OsamaAlsahli/data-glove/images/gantt_chart.png

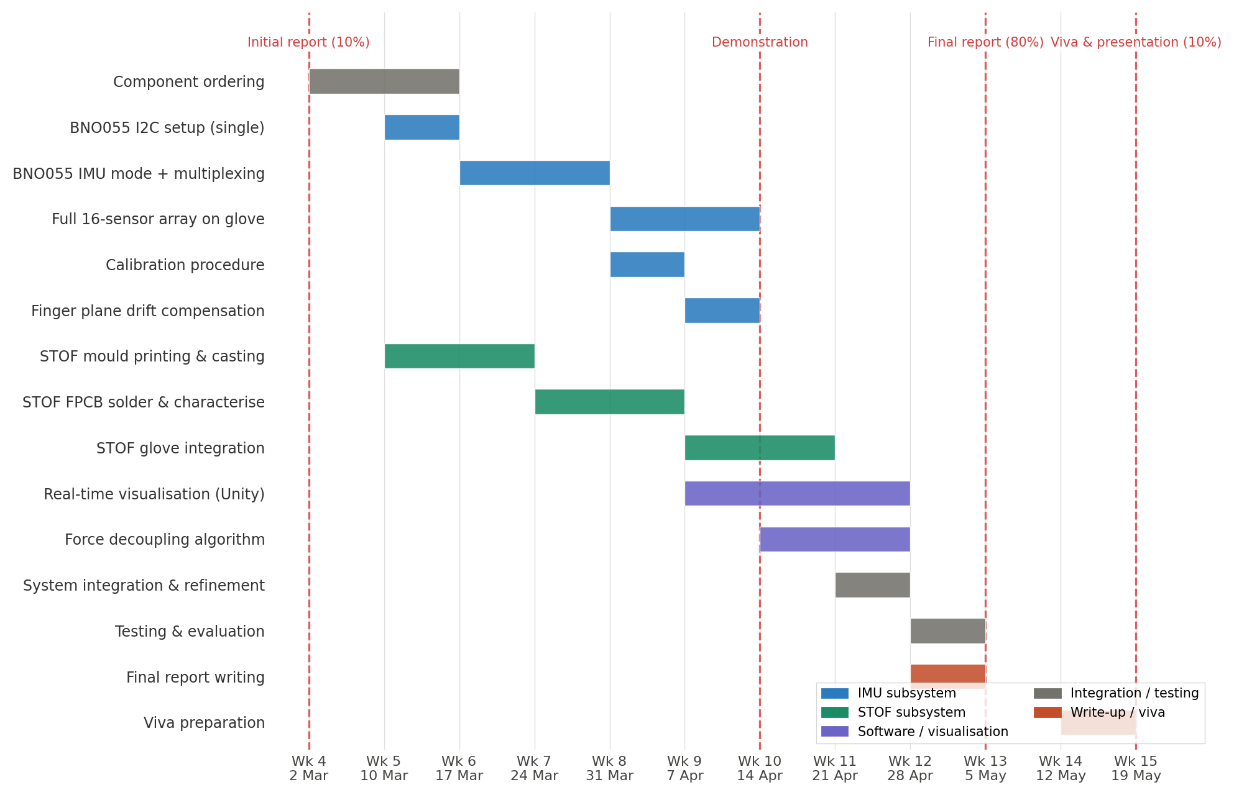
images/gantt_chart.png
