OsamaAlsahli/data-glove/images/PXL_20260508_102140044.jpg

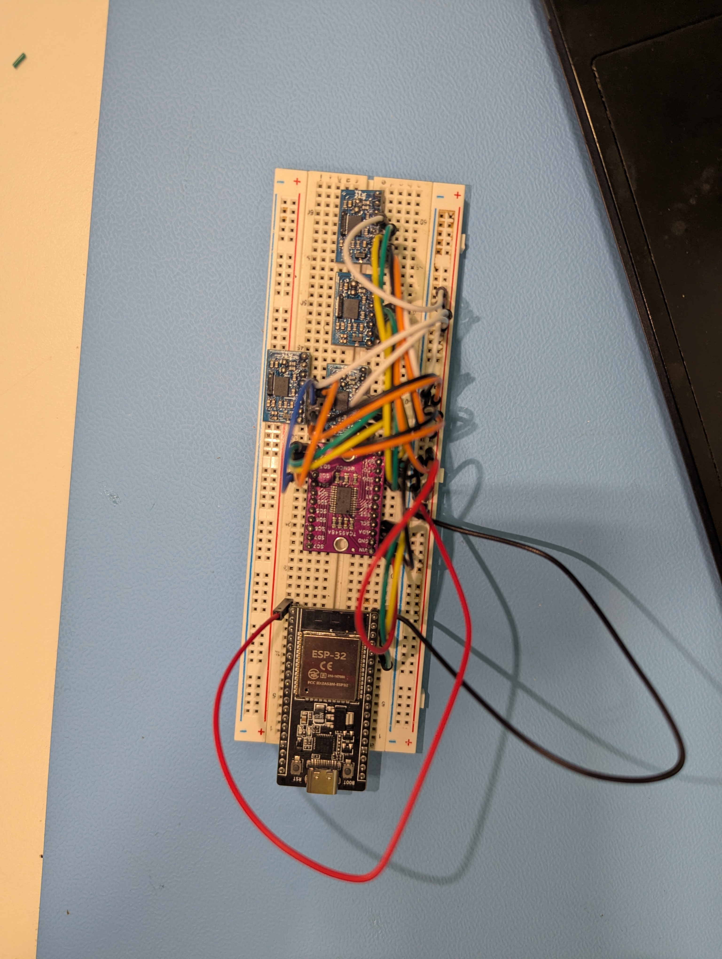
images/PXL_20260508_102140044.jpg
