OsamaAlsahli/data-glove/images/PXL_20260508_141840744.jpg

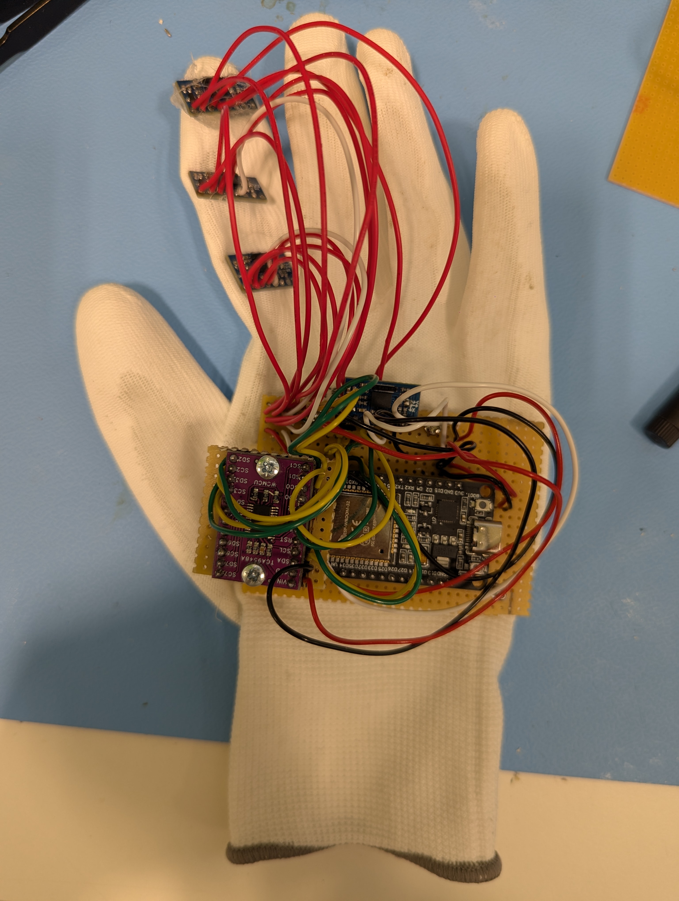
images/PXL_20260508_141840744.jpg
