OsamaAlsahli/data-glove/images/PXL_20260508_141846778.jpg

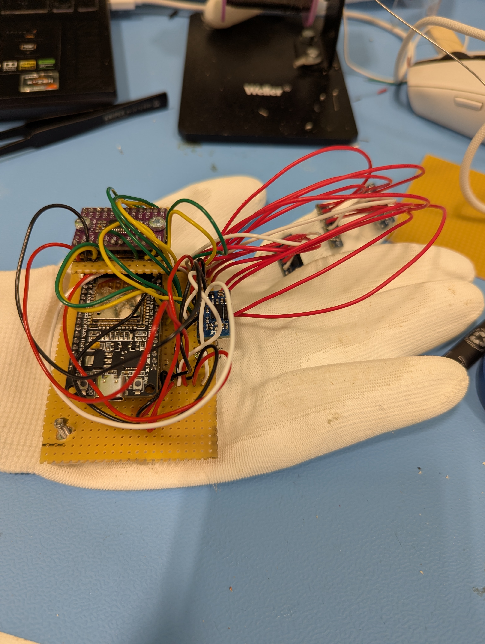
images/PXL_20260508_141846778.jpg
