OsamaAlsahli/data-glove/images/PXL_20260508_141911992.jpg

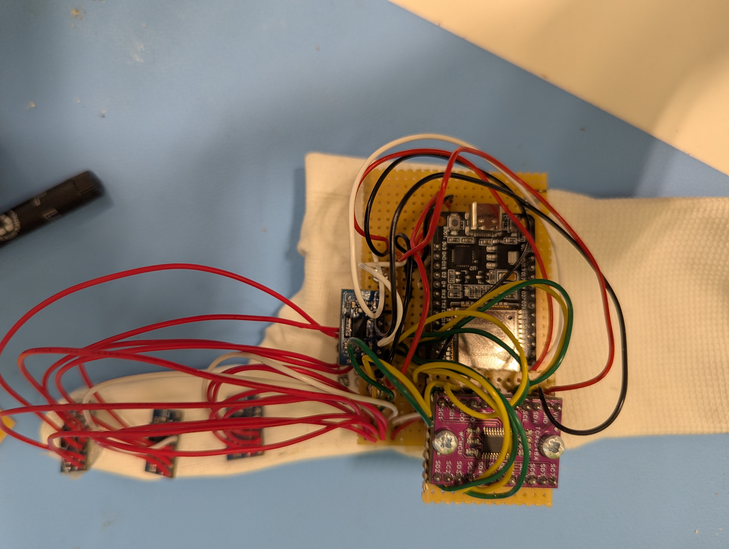
images/PXL_20260508_141911992.jpg
