OsamaAlsahli/data-glove/images/PXL_20260508_141916743.jpg

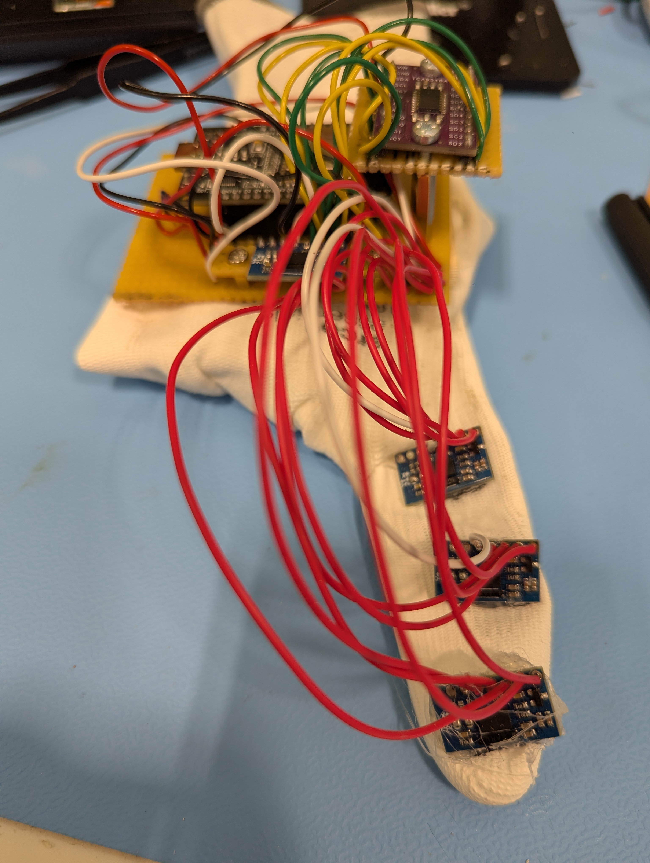
images/PXL_20260508_141916743.jpg
