OsamaAlsahli/data-glove/images/PXL_20260508_141919534.jpg

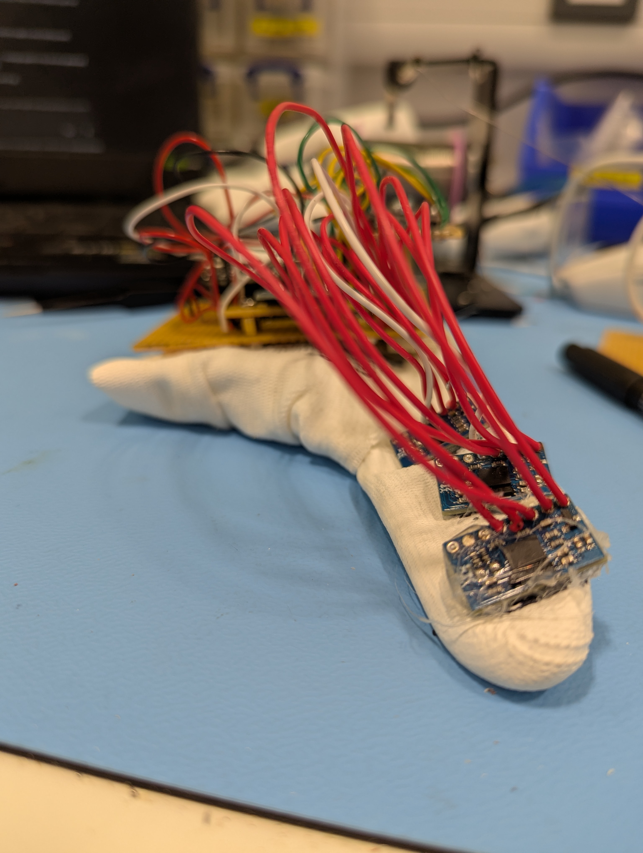
images/PXL_20260508_141919534.jpg
