OsamaAlsahli/data-glove/images/PXL_20260508_141922260.jpg

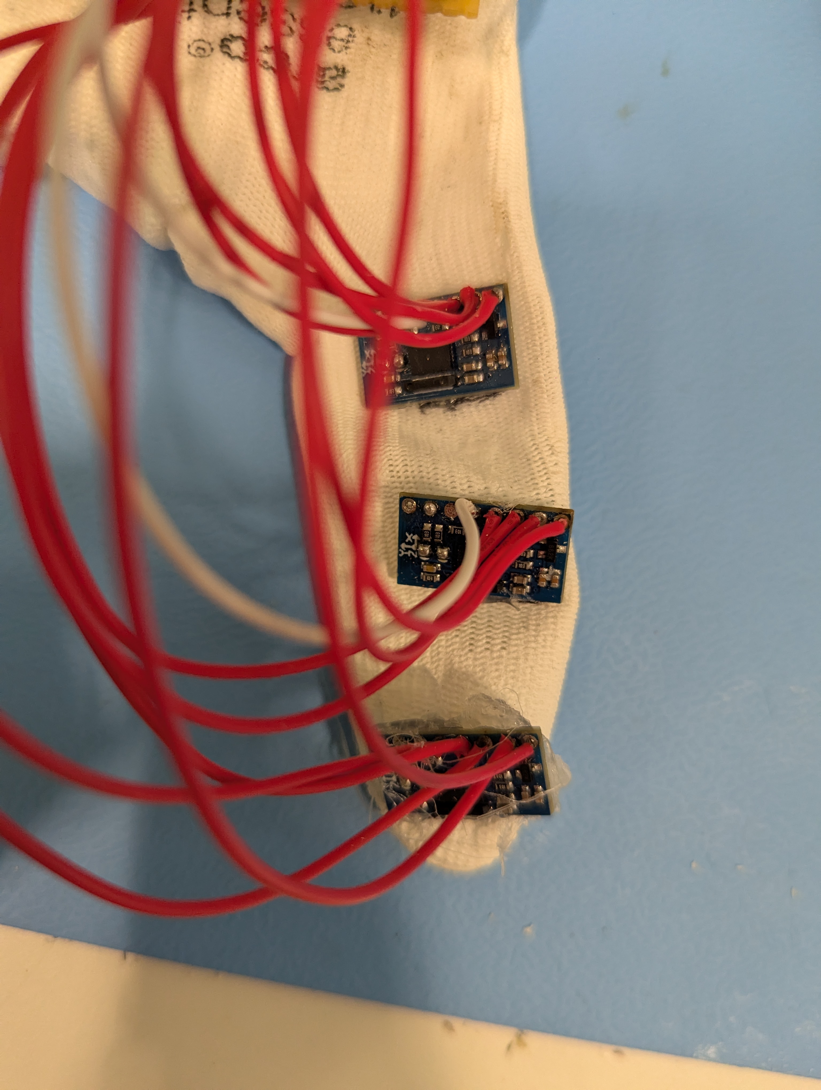
images/PXL_20260508_141922260.jpg
