OsamaAlsahli/data-glove/images/PXL_20260508_142635021.jpg

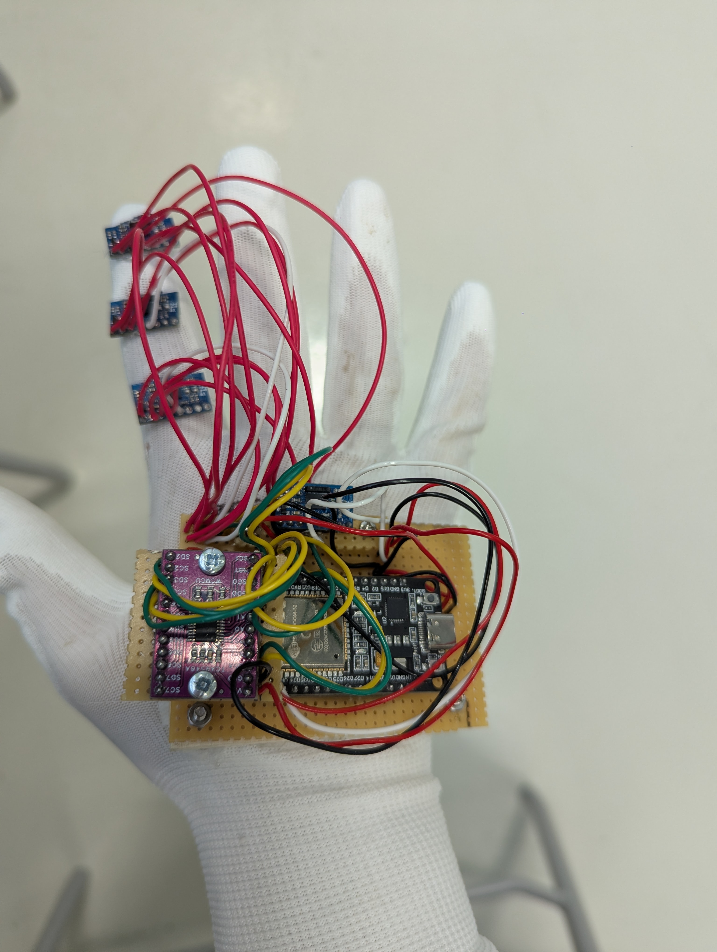
images/PXL_20260508_142635021.jpg
