OsamaAlsahli/data-glove/images/PXL_20260508_142637058.jpg

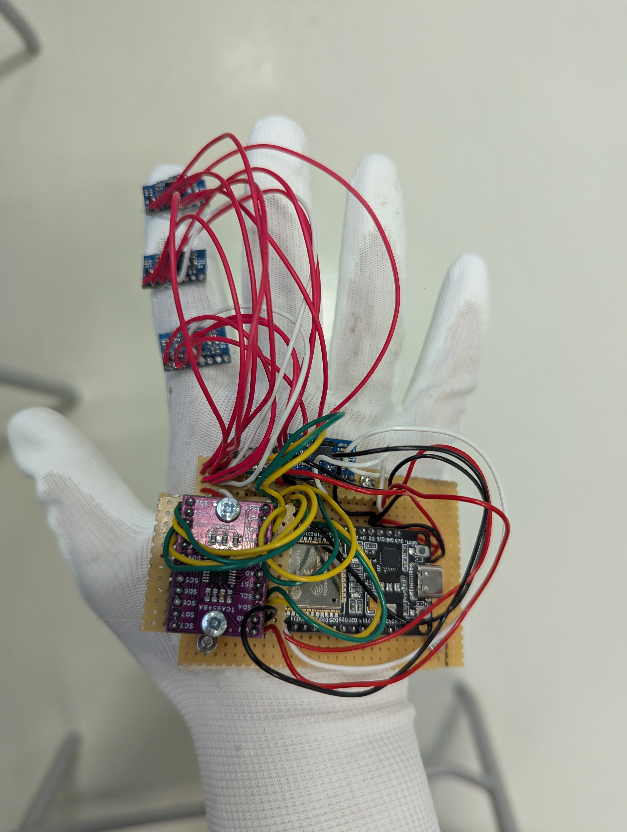
images/PXL_20260508_142637058.jpg
