OsamaAlsahli/data-glove/images/PXL_20260508_142641269.jpg

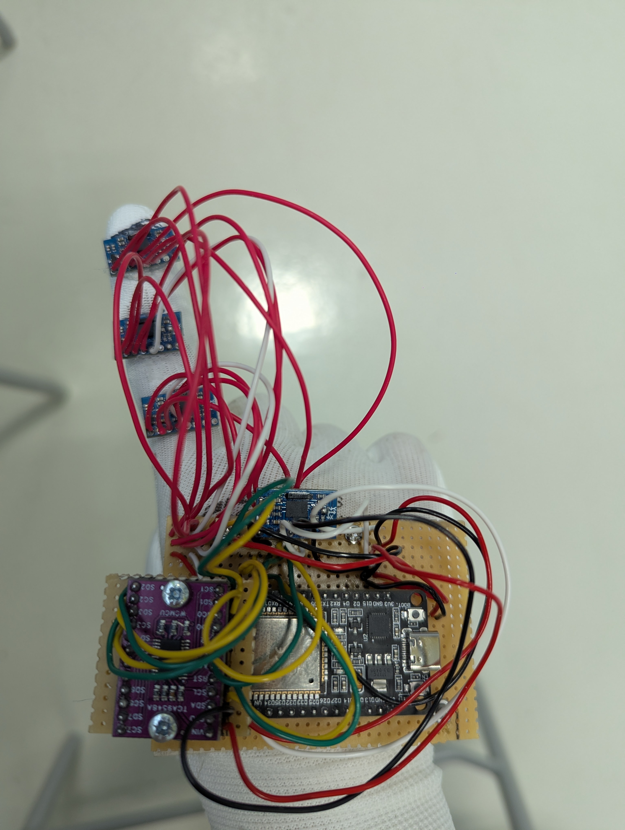
images/PXL_20260508_142641269.jpg
