OsamaAlsahli/data-glove/images/PXL_20260508_142649193.jpg

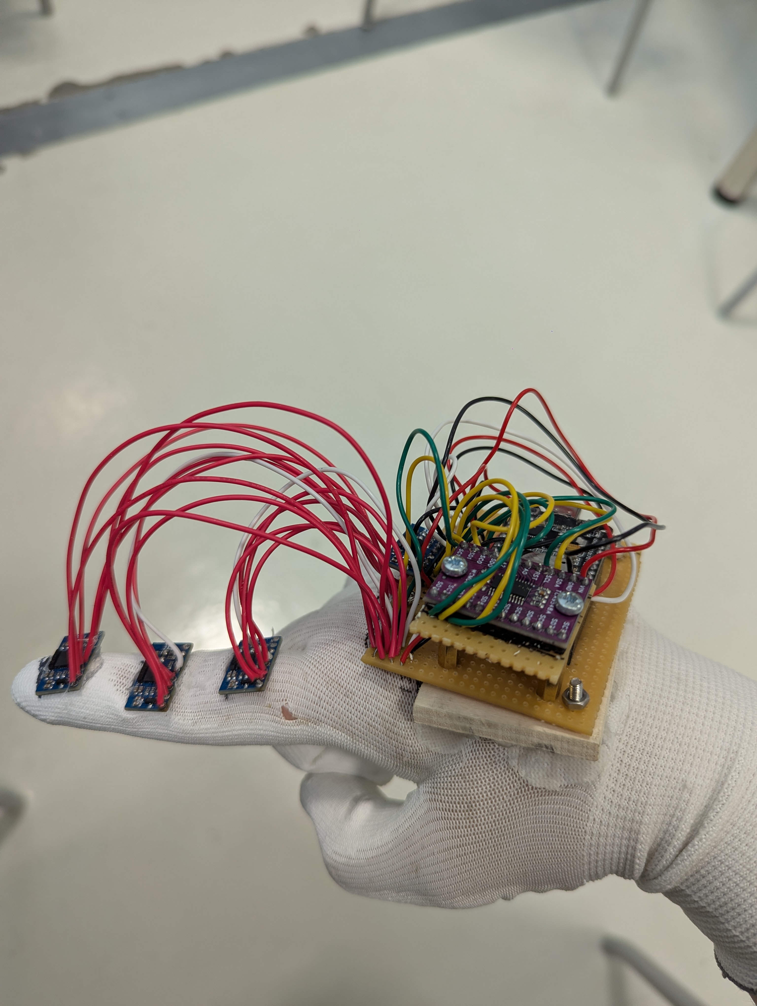
images/PXL_20260508_142649193.jpg
