OsamaAlsahli/data-glove/images/PXL_20260508_142710227.jpg

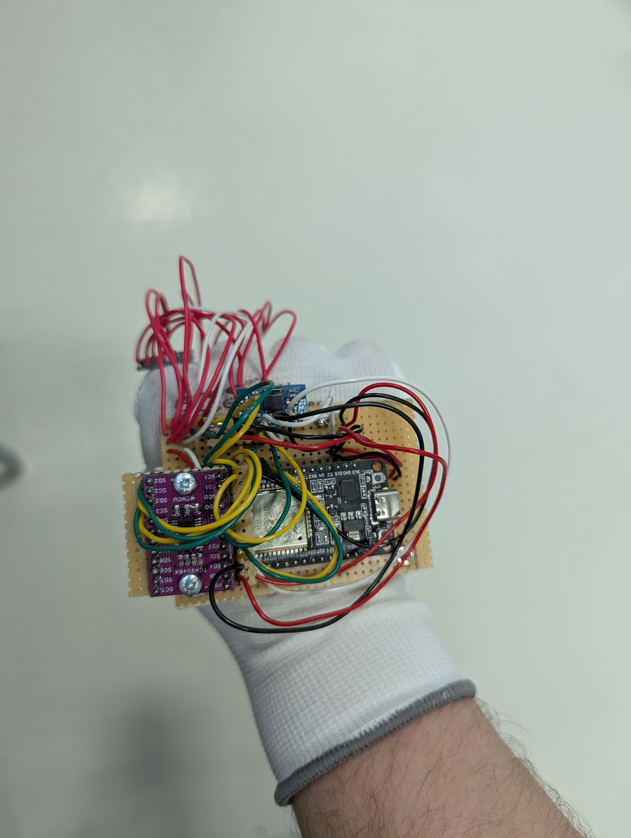
images/PXL_20260508_142710227.jpg
