OsamaAlsahli/data-glove/images/PXL_20260517_213951667.jpg

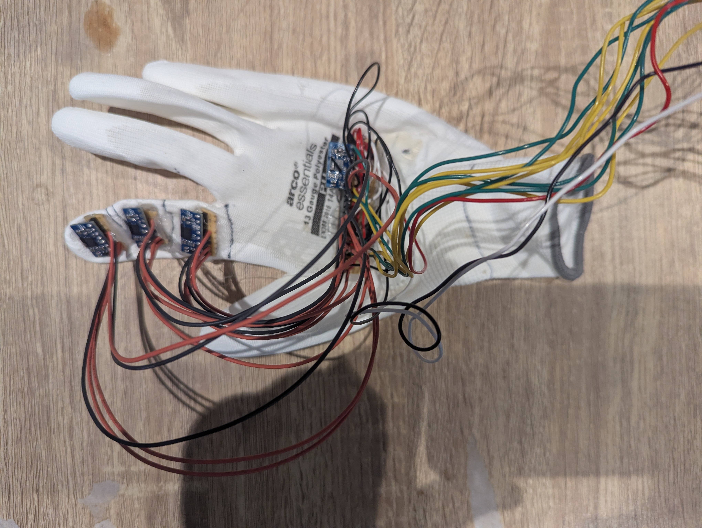
images/PXL_20260517_213951667.jpg
