OsamaAlsahli/data-glove/images/PXL_20260517_214013301.jpg

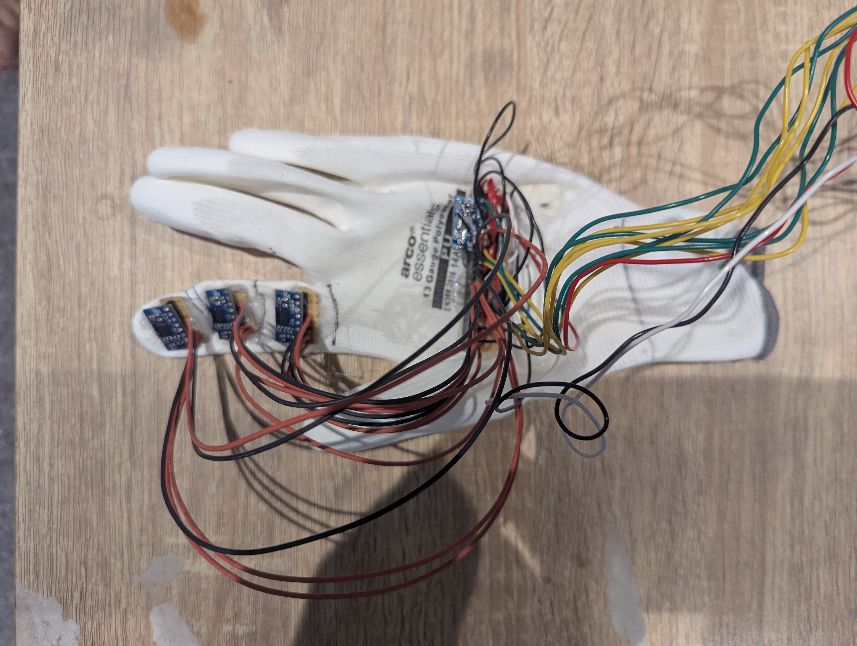
images/PXL_20260517_214013301.jpg
