OsamaAlsahli/data-glove/images/PXL_20260517_214023272.jpg

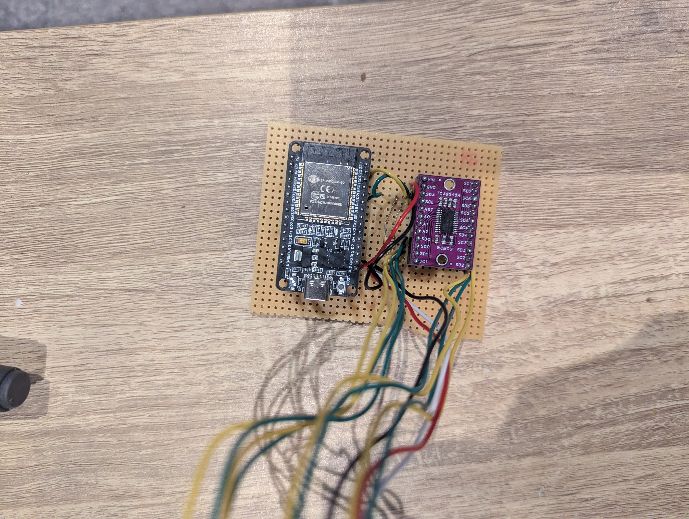
images/PXL_20260517_214023272.jpg
