OsamaAlsahli/data-glove/images/PXL_20260517_214024395.jpg

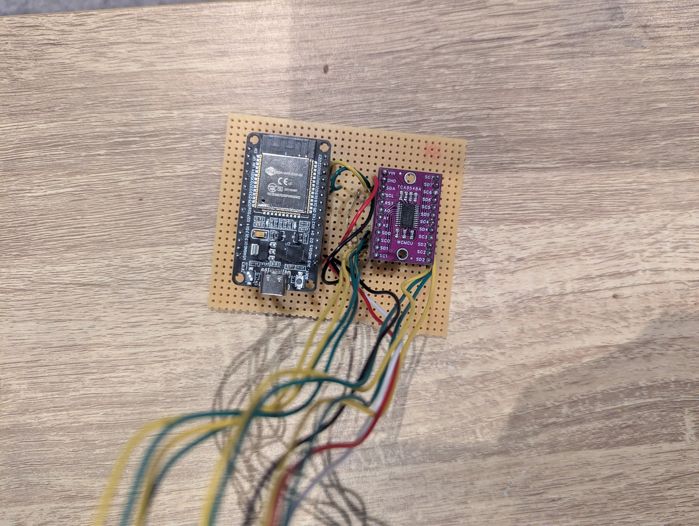
images/PXL_20260517_214024395.jpg
