OsamaAlsahli/data-glove/images/PXL_20260517_214100365.jpg

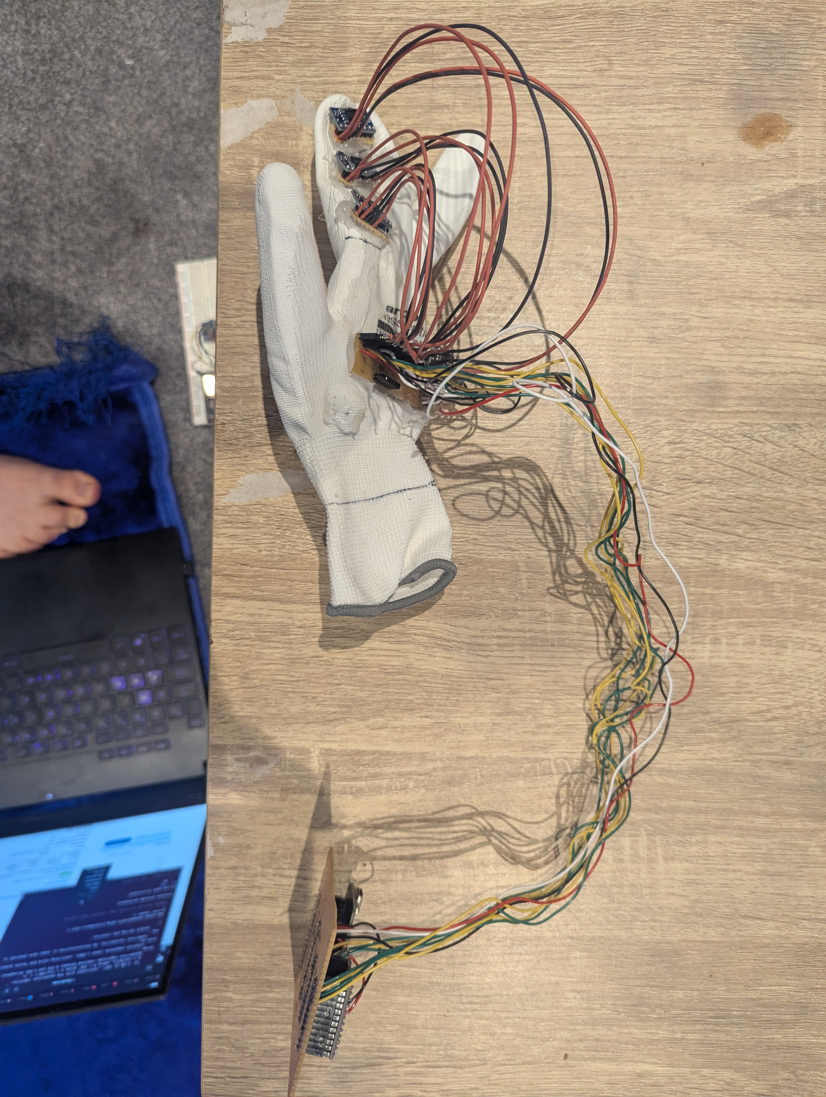
images/PXL_20260517_214100365.jpg
