OsamaAlsahli/data-glove/images/PXL_20260517_214147639.jpg

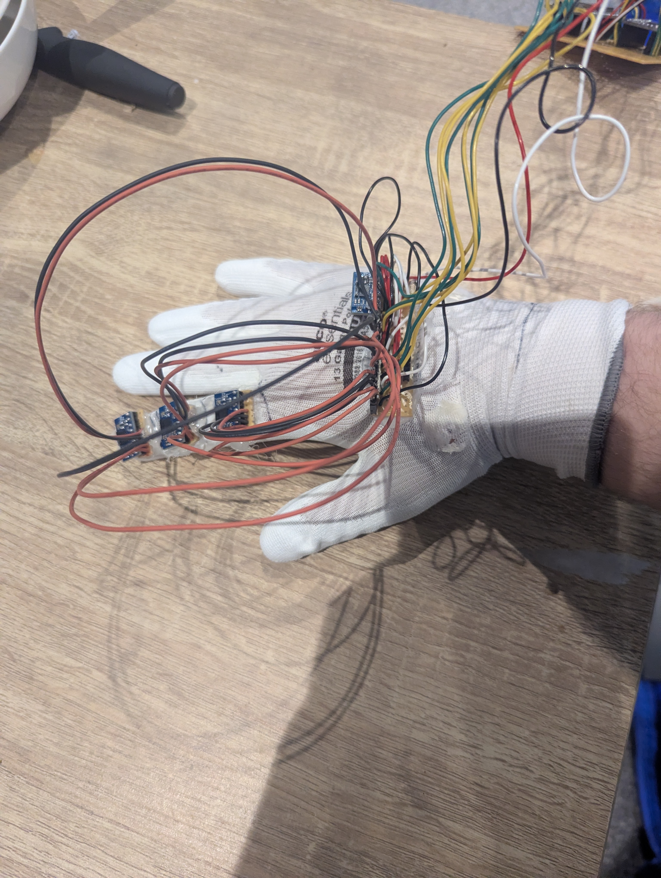
images/PXL_20260517_214147639.jpg
