OsamaAlsahli/data-glove/images/PXL_20260517_214149598.jpg

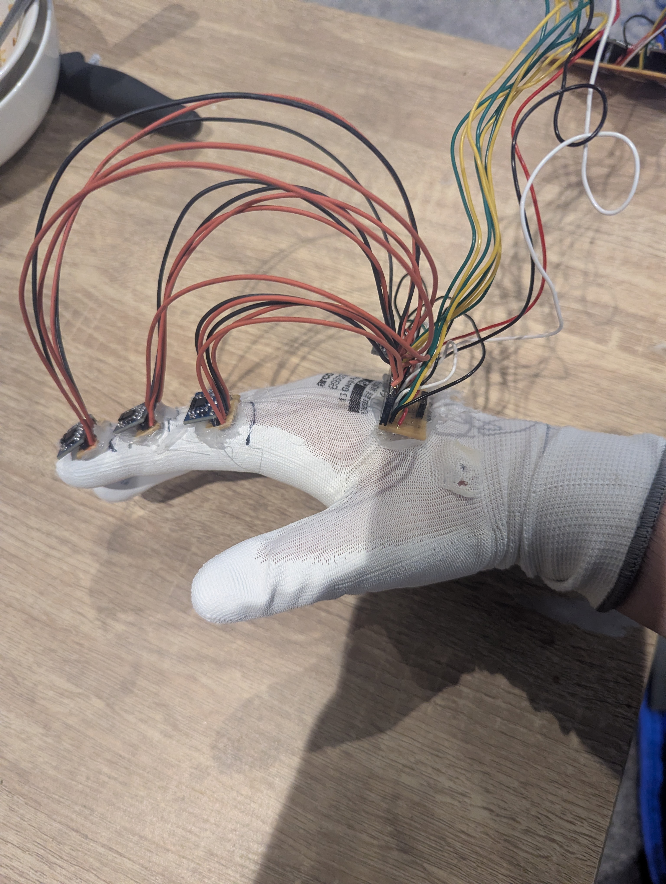
images/PXL_20260517_214149598.jpg
