OsamaAlsahli/data-glove/images/Screenshot from 2026-05-17 22-49-18.png

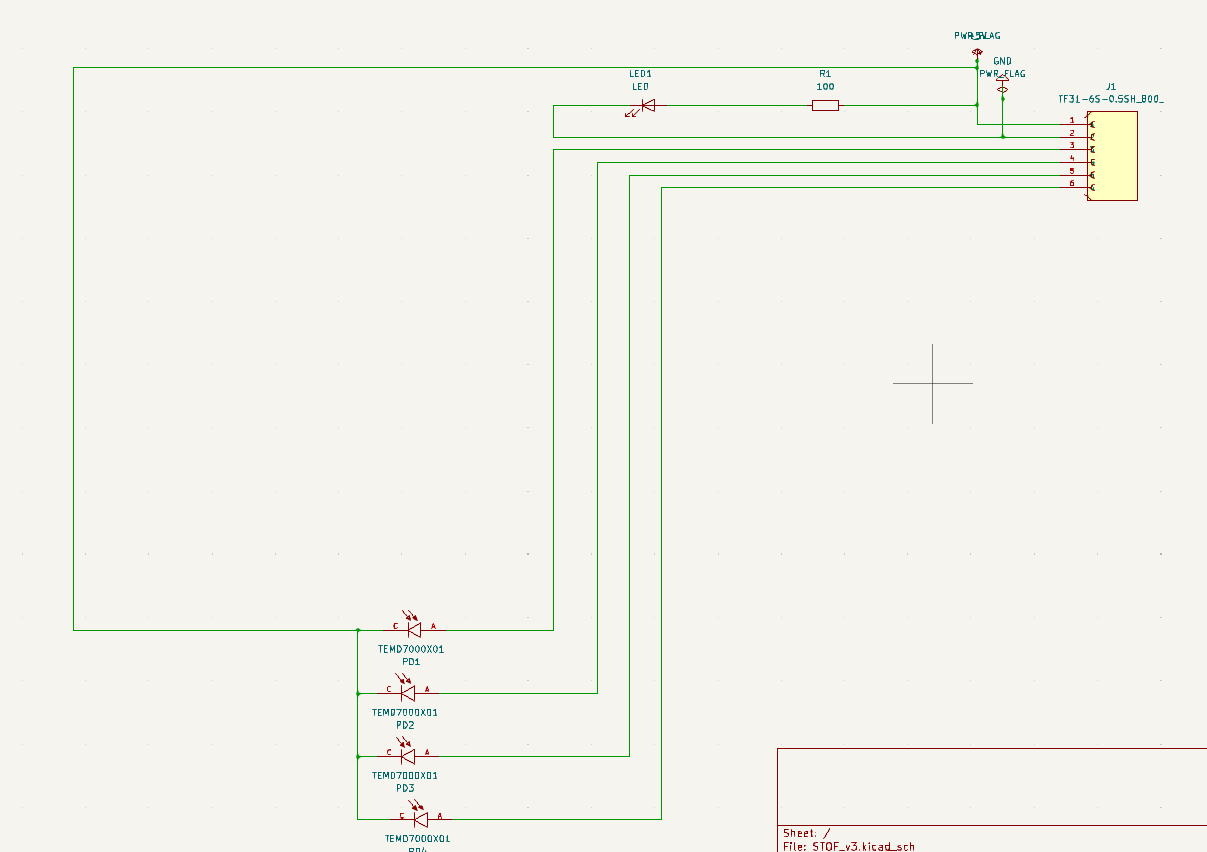
images/Screenshot from 2026-05-17 22-49-18.png
